gsuckz/pll/tex/images/image21.jpg

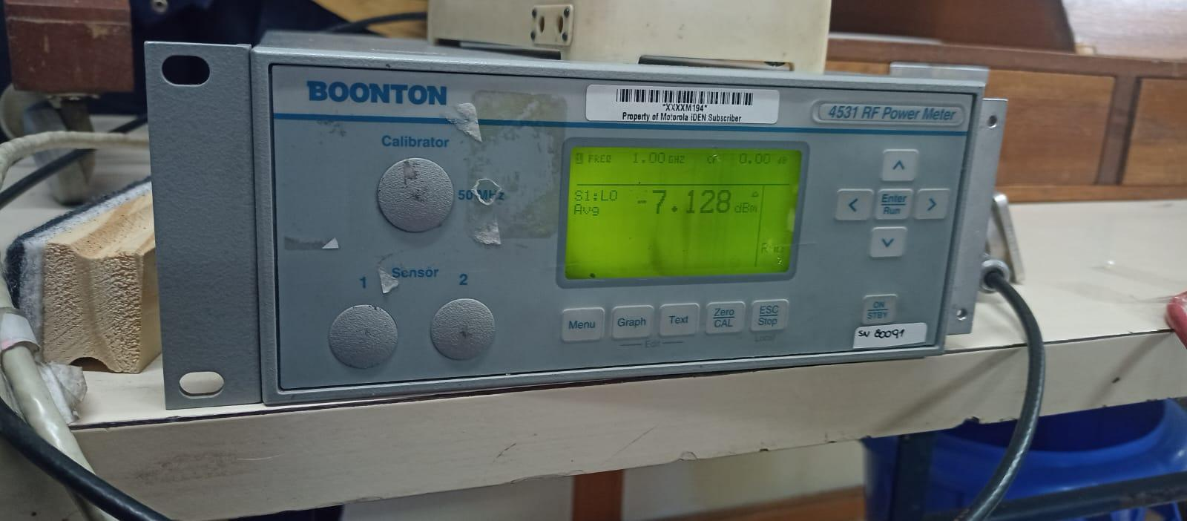
tex/images/image21.jpg
