gsuckz/pll/tex/images/image24.png

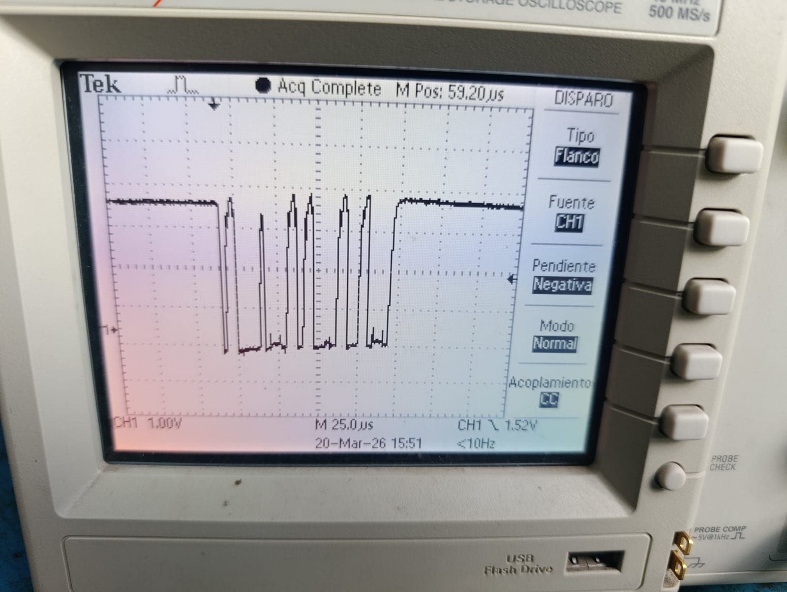
tex/images/image24.png
