gsuckz/pll/tex/images/image35.png

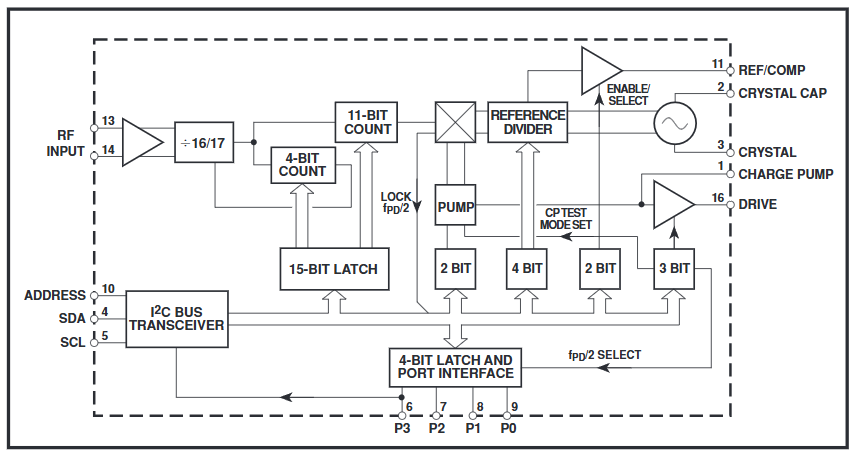
tex/images/image35.png
