gsuckz/pll/tex/images/image36.png

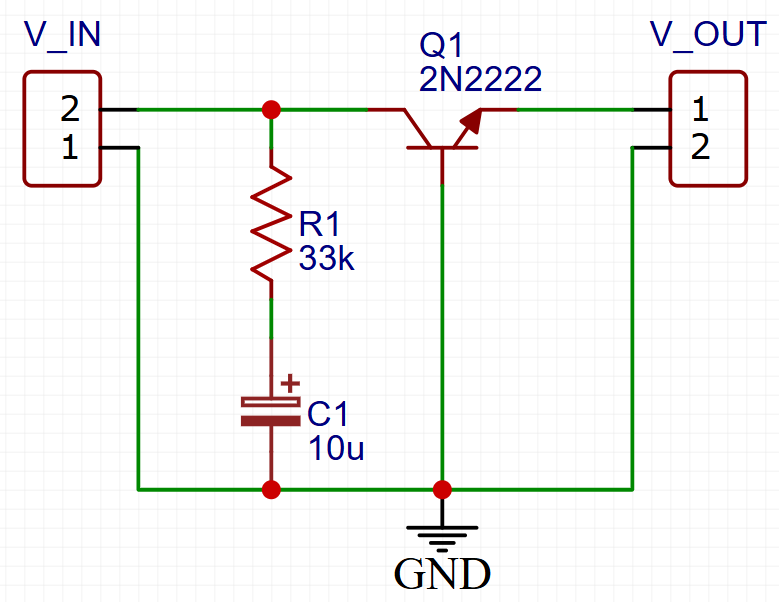
tex/images/image36.png
