gsuckz/pll/tex/img/Esquema de conexion.png

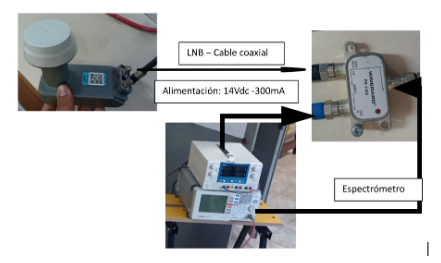
tex/img/Esquema de conexion.png
