gsuckz/pll/tex/img/LNB Dual.png

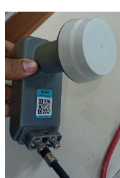
tex/img/LNB Dual.png
