gsuckz/pll/tex/img/Transmision y deteccion de la señal 1.png

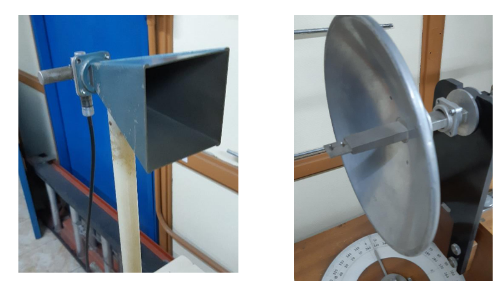
tex/img/Transmision y deteccion de la señal 1.png
