gsuckz/pll/tex/img/Transmision y deteccion de la señal 2.png

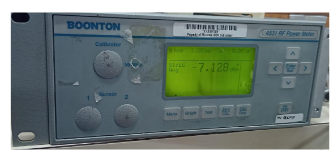
tex/img/Transmision y deteccion de la señal 2.png
